jeffqchen/Famicom-Expansion-Port-Switcher/pics/Famicom/GPM/case_crack_01.jpg

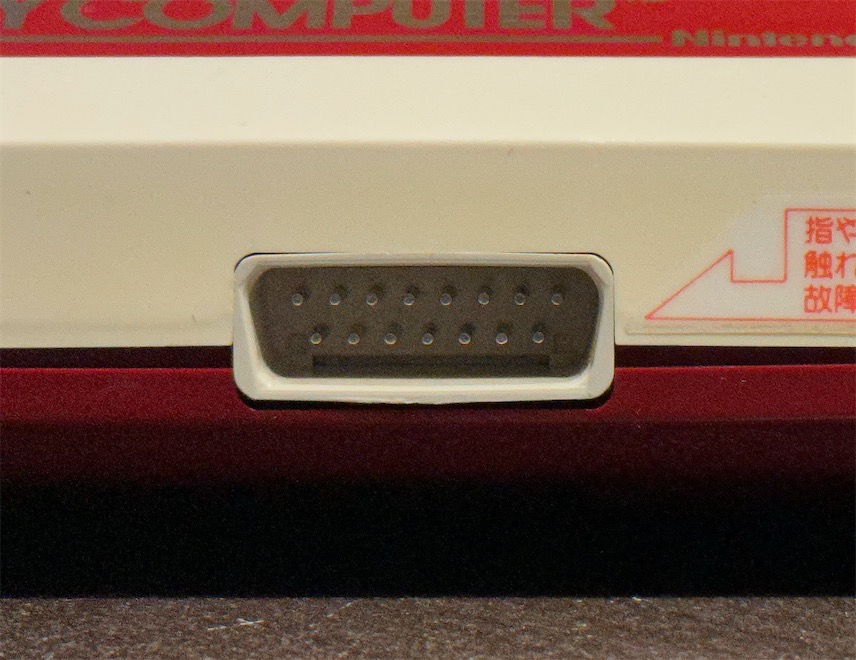
pics/Famicom/GPM/case_crack_01.jpg
