jeffqchen/Famicom-Expansion-Port-Switcher/pics/Famicom/GPM/case_crack_02.jpg

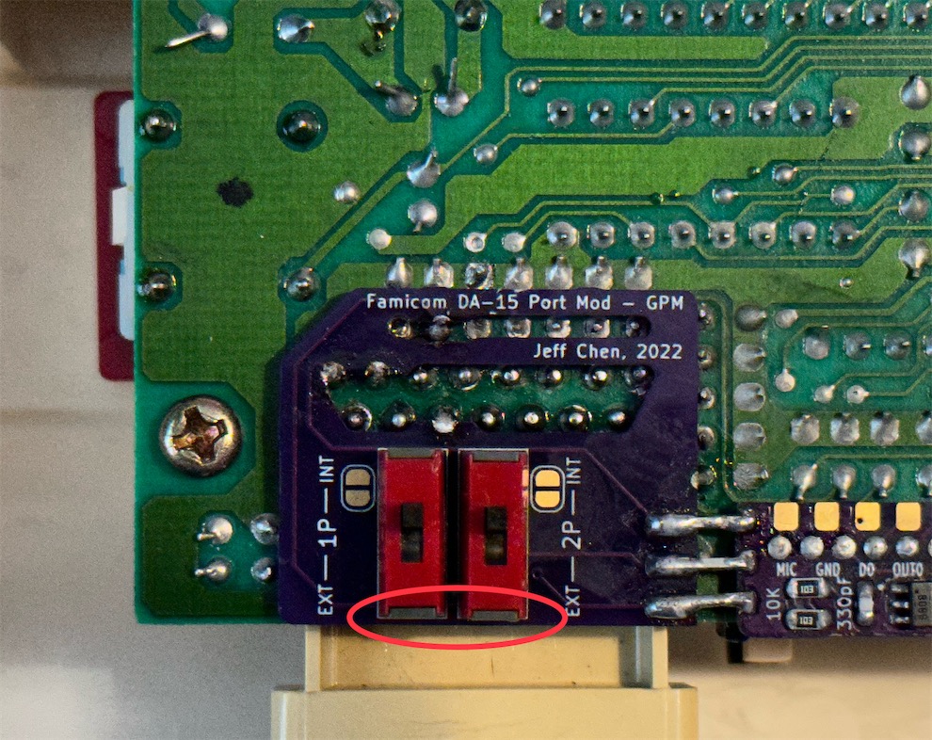
pics/Famicom/GPM/case_crack_02.jpg
