jeffqchen/Famicom-Expansion-Port-Switcher/pics/Famicom/GPM/cuttrace.jpg

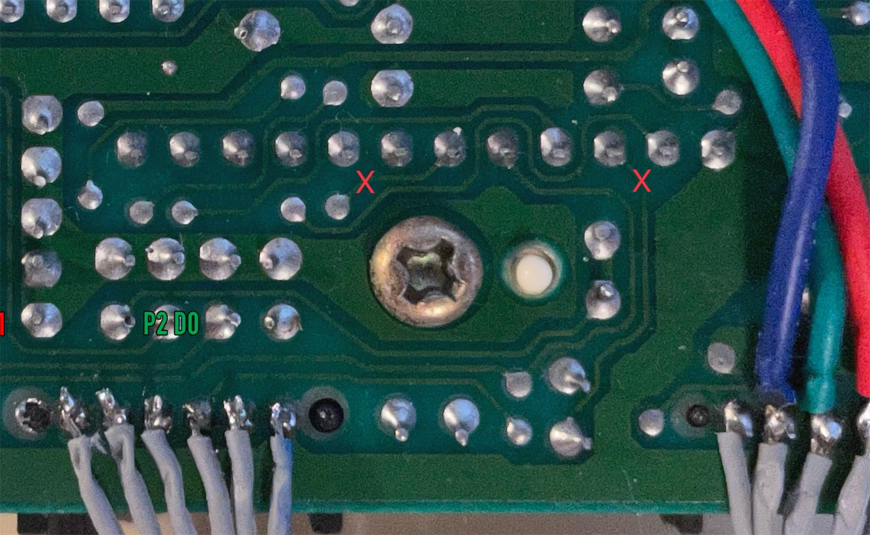
pics/Famicom/GPM/cuttrace.jpg
