jeffqchen/Famicom-Expansion-Port-Switcher/pics/Famicom/GPM/da15_isolate.jpg

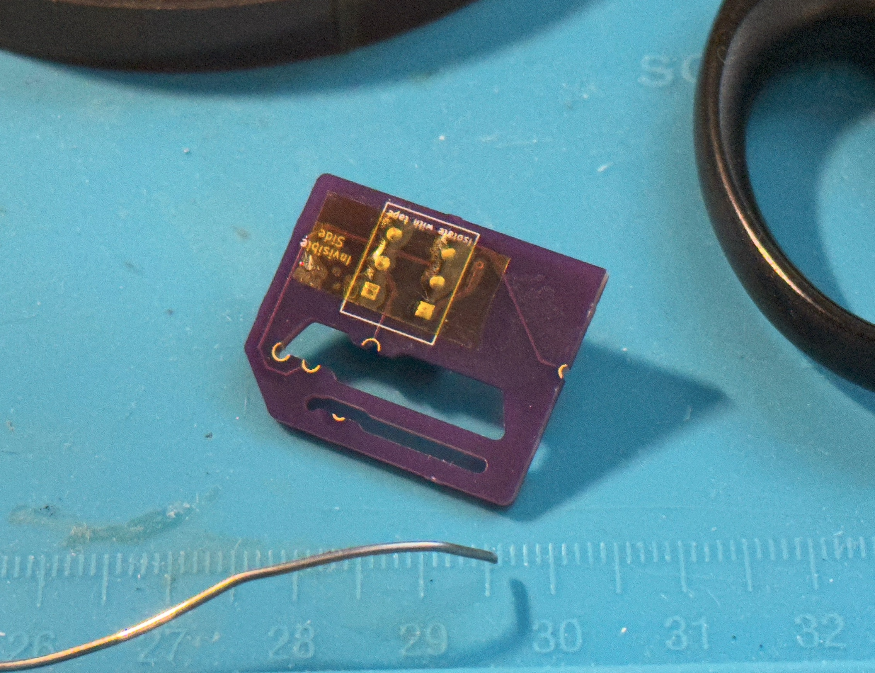
pics/Famicom/GPM/da15_isolate.jpg
