jeffqchen/Famicom-Expansion-Port-Switcher/pics/Famicom/GPM/da15_populate.jpg

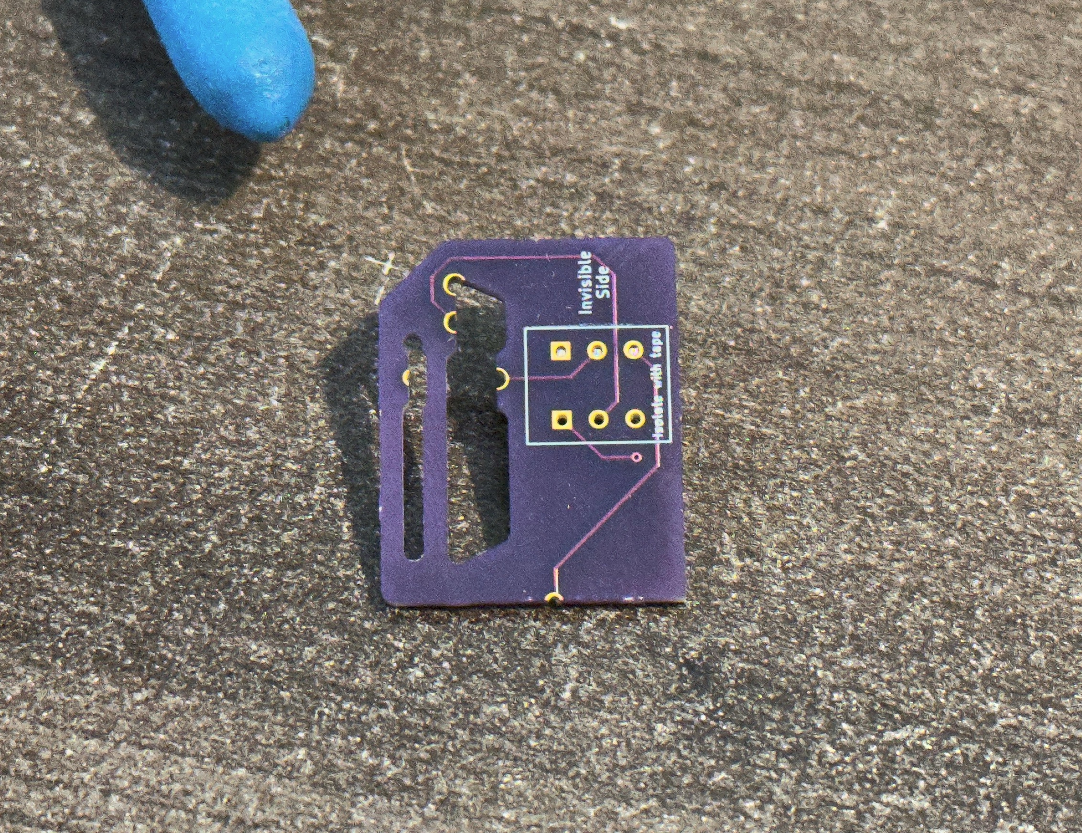
pics/Famicom/GPM/da15_populate.jpg
