jeffqchen/Famicom-Expansion-Port-Switcher/pics/Famicom/GPM/drill_01_intention.jpg

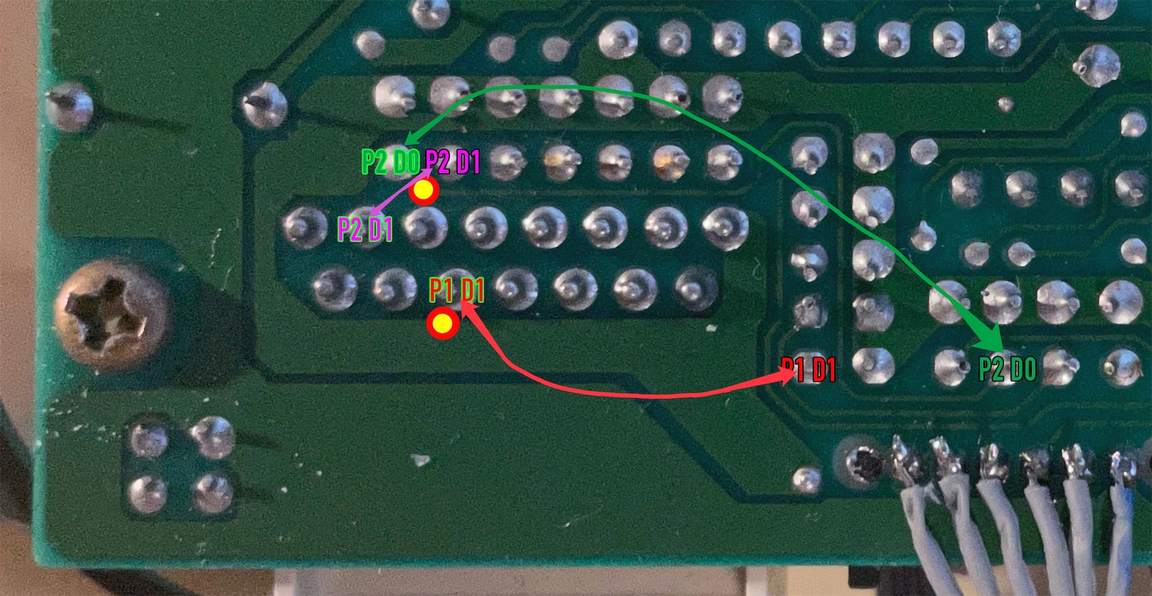
pics/Famicom/GPM/drill_01_intention.jpg
