jeffqchen/Famicom-Expansion-Port-Switcher/pics/Famicom/GPM/drill_02_withjig.jpg

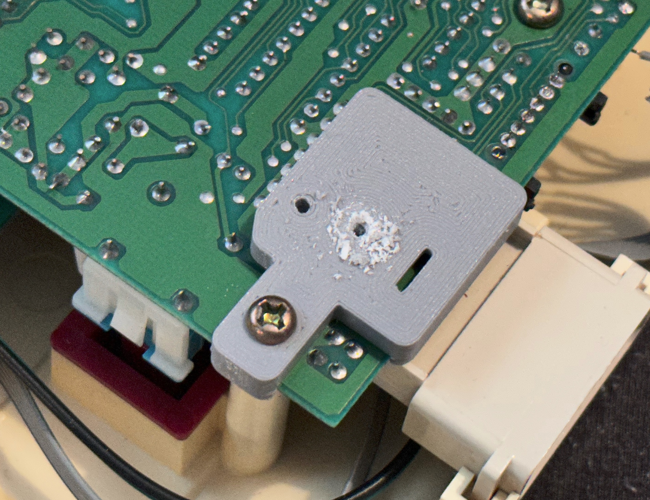
pics/Famicom/GPM/drill_02_withjig.jpg
