jeffqchen/Famicom-Expansion-Port-Switcher/pics/Famicom/GPM/drill_03_afterwards.jpg

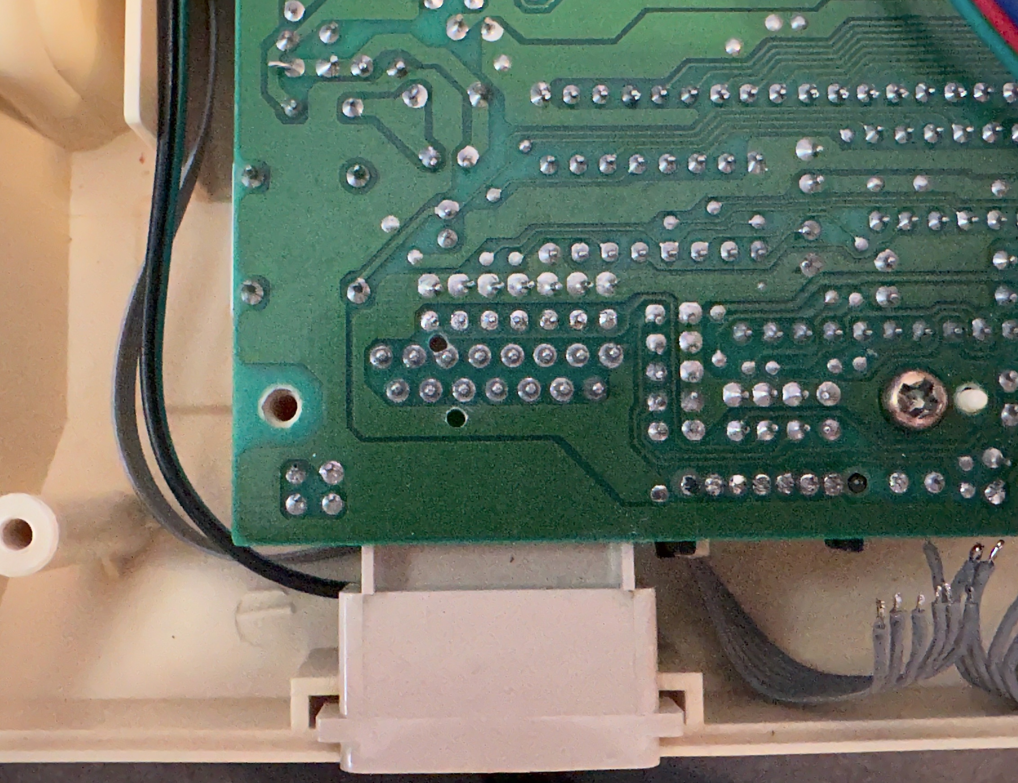
pics/Famicom/GPM/drill_03_afterwards.jpg
