jeffqchen/Famicom-Expansion-Port-Switcher/pics/Famicom/GPM/dryfit_02.jpg

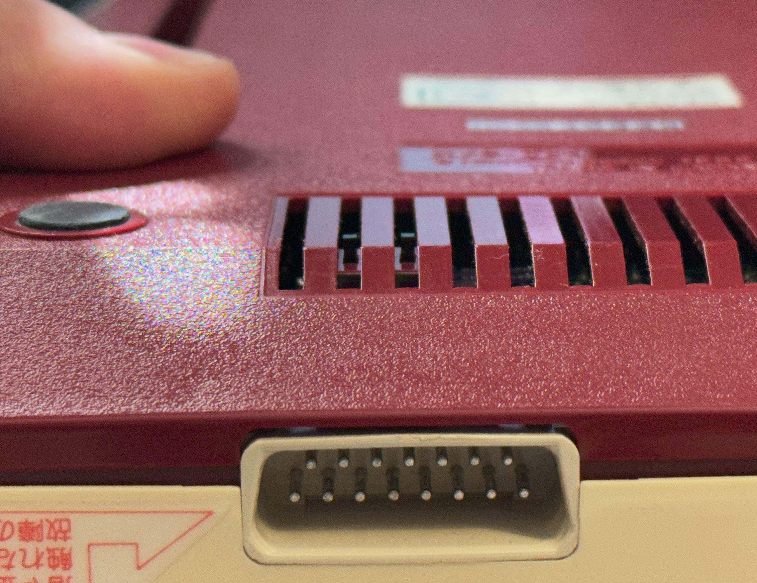
pics/Famicom/GPM/dryfit_02.jpg
