jeffqchen/Famicom-Expansion-Port-Switcher/pics/Famicom/GPM/finish.jpg

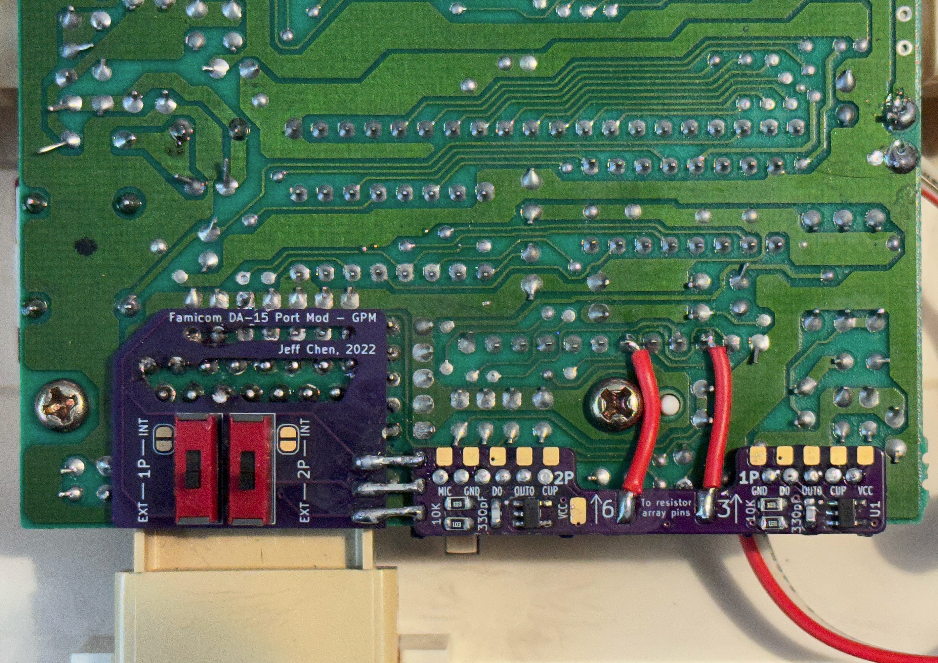
pics/Famicom/GPM/finish.jpg
