jeffqchen/Famicom-Expansion-Port-Switcher/pics/Famicom/GPM/functionality.jpg

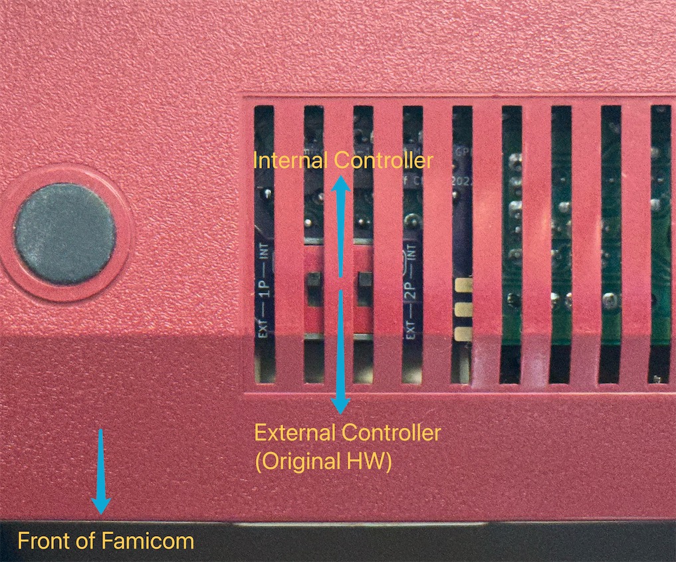
pics/Famicom/GPM/functionality.jpg
