jeffqchen/Famicom-Expansion-Port-Switcher/pics/Famicom/GPM/internalpcb_hack.jpg

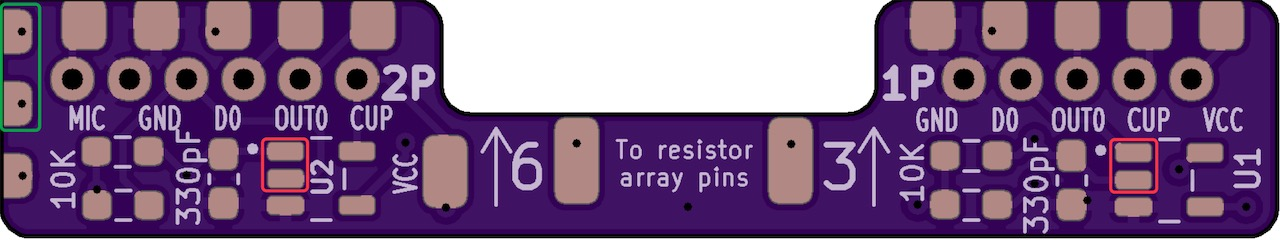
pics/Famicom/GPM/internalpcb_hack.jpg
