jeffqchen/Famicom-Expansion-Port-Switcher/pics/Famicom/GPM/internalpcb_populate.jpg

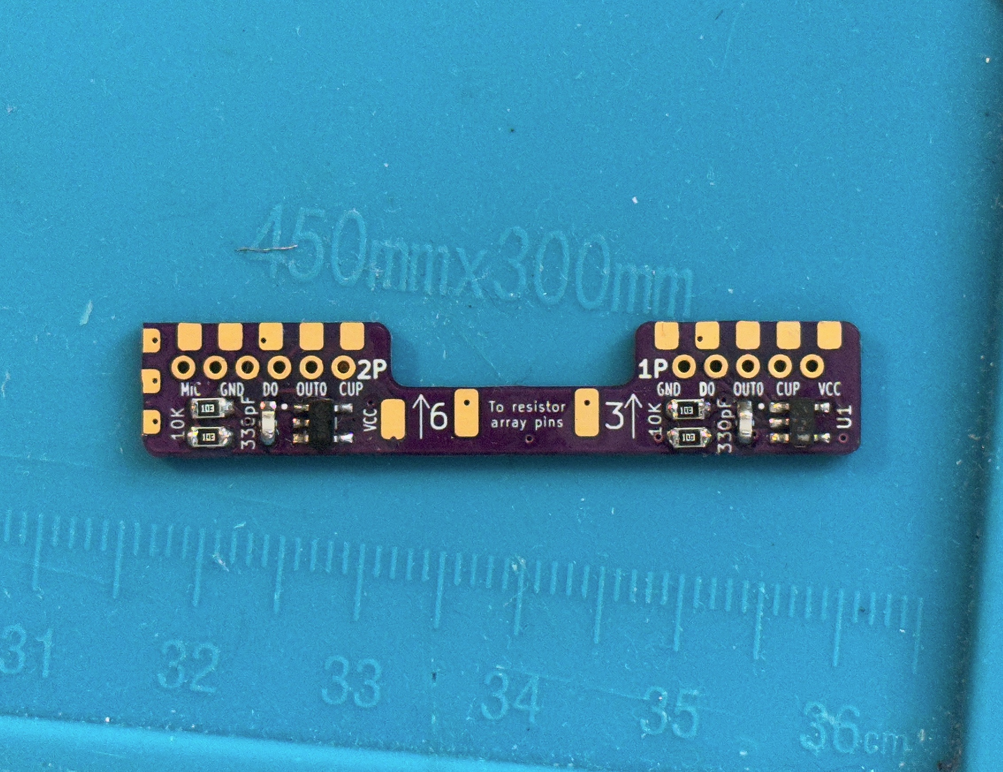
pics/Famicom/GPM/internalpcb_populate.jpg
