jeffqchen/Famicom-Expansion-Port-Switcher/pics/Famicom/GPM/jig.jpg

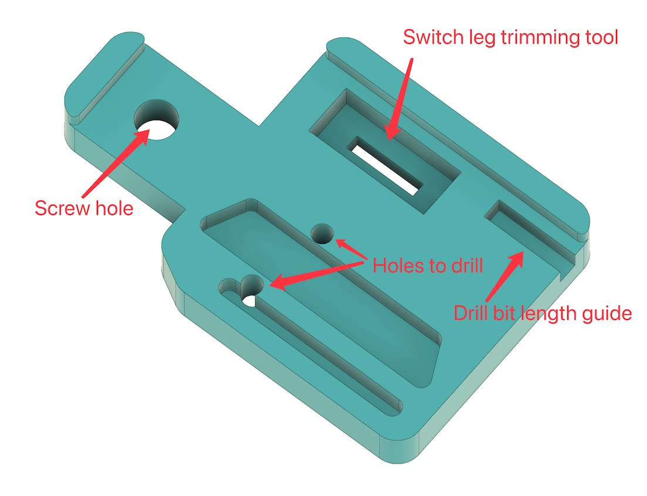
pics/Famicom/GPM/jig.jpg
