jeffqchen/Famicom-Expansion-Port-Switcher/pics/Famicom/GPM/straightenpins_02.jpg

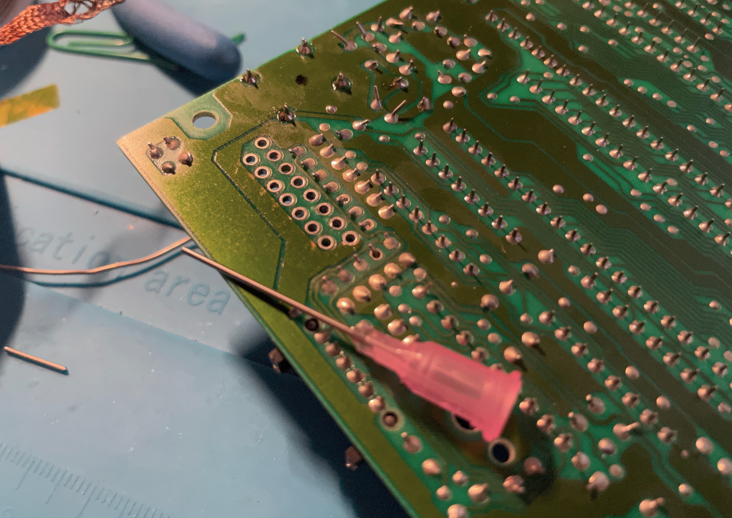
pics/Famicom/GPM/straightenpins_02.jpg
