jeffqchen/Famicom-Expansion-Port-Switcher/pics/Famicom/GPM/straightenpins_03.jpg

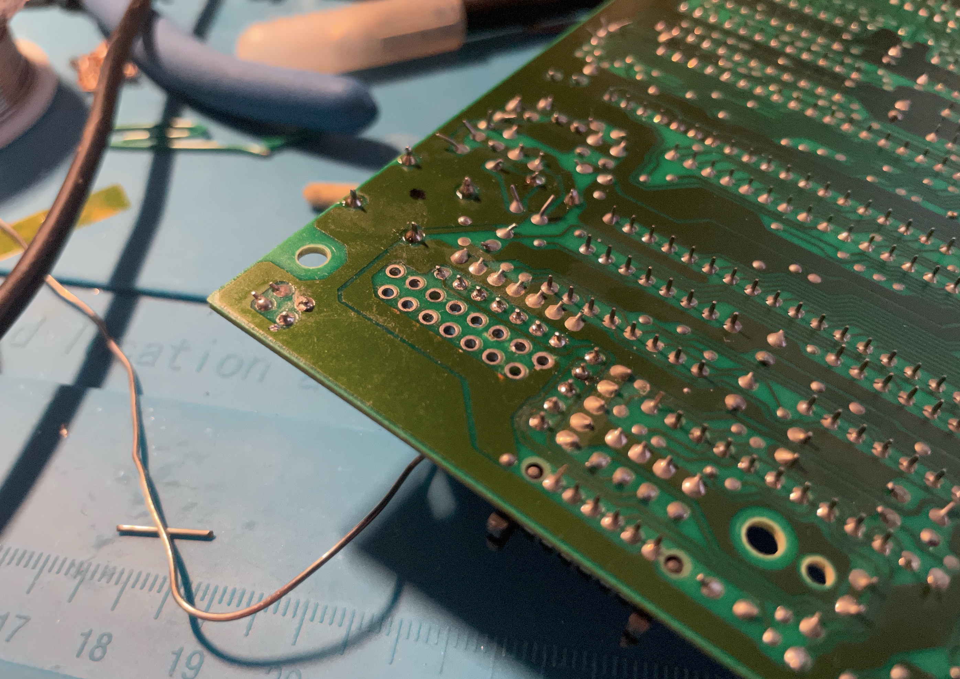
pics/Famicom/GPM/straightenpins_03.jpg
