jeffqchen/Famicom-Expansion-Port-Switcher/pics/Famicom/GPM/trim_01.jpg

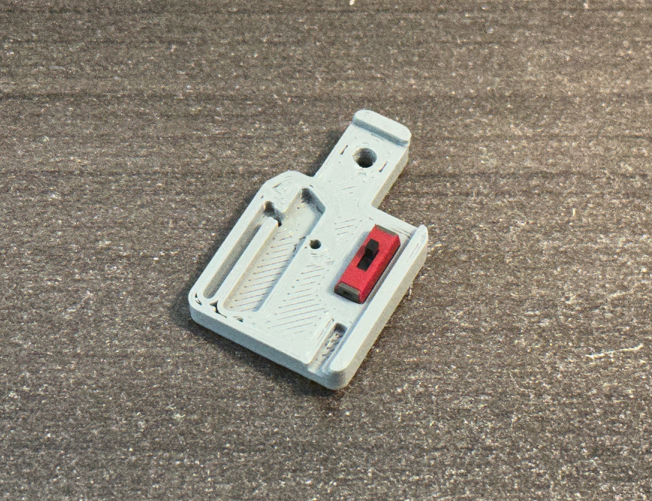
pics/Famicom/GPM/trim_01.jpg
