jeffqchen/Famicom-Expansion-Port-Switcher/pics/front_expansion.jpg

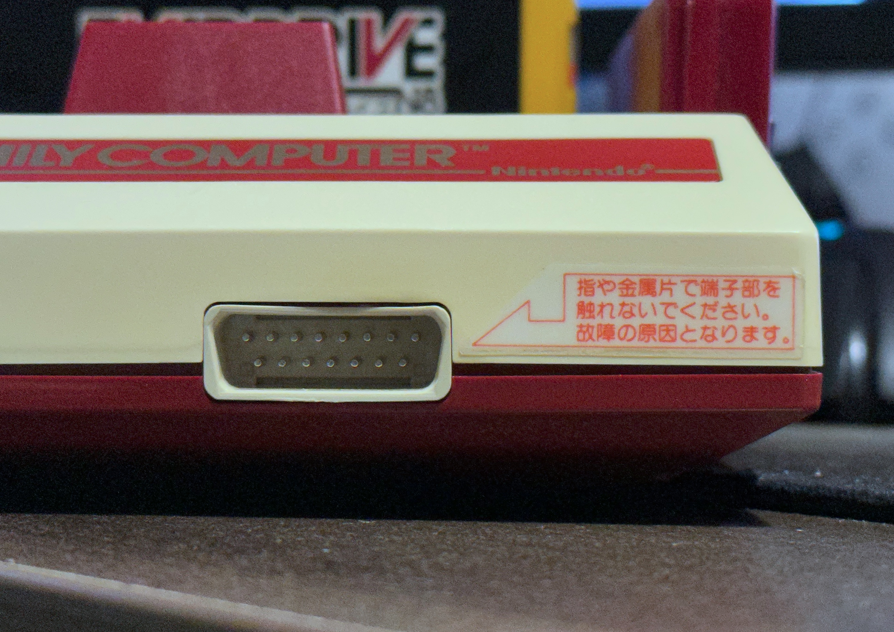
pics/front_expansion.jpg
