jeffqchen/Famicom-Expansion-Port-Switcher/pics/Twins/functionality.jpg

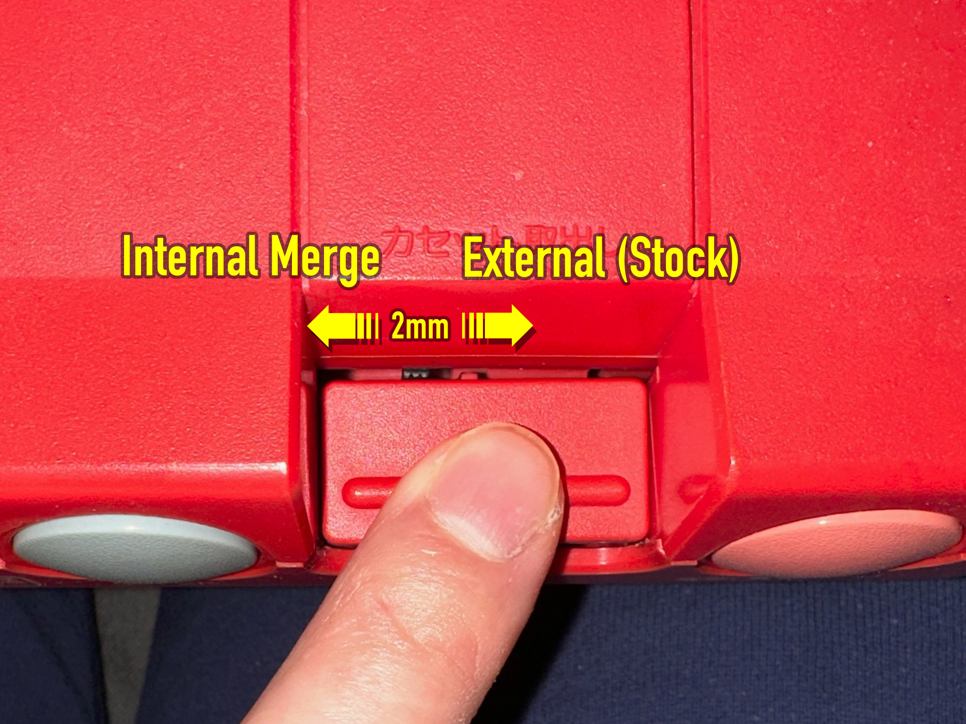
pics/Twins/functionality.jpg
