jeffqchen/Famicom-Expansion-Port-Switcher/pics/Twins/main_PCB.png

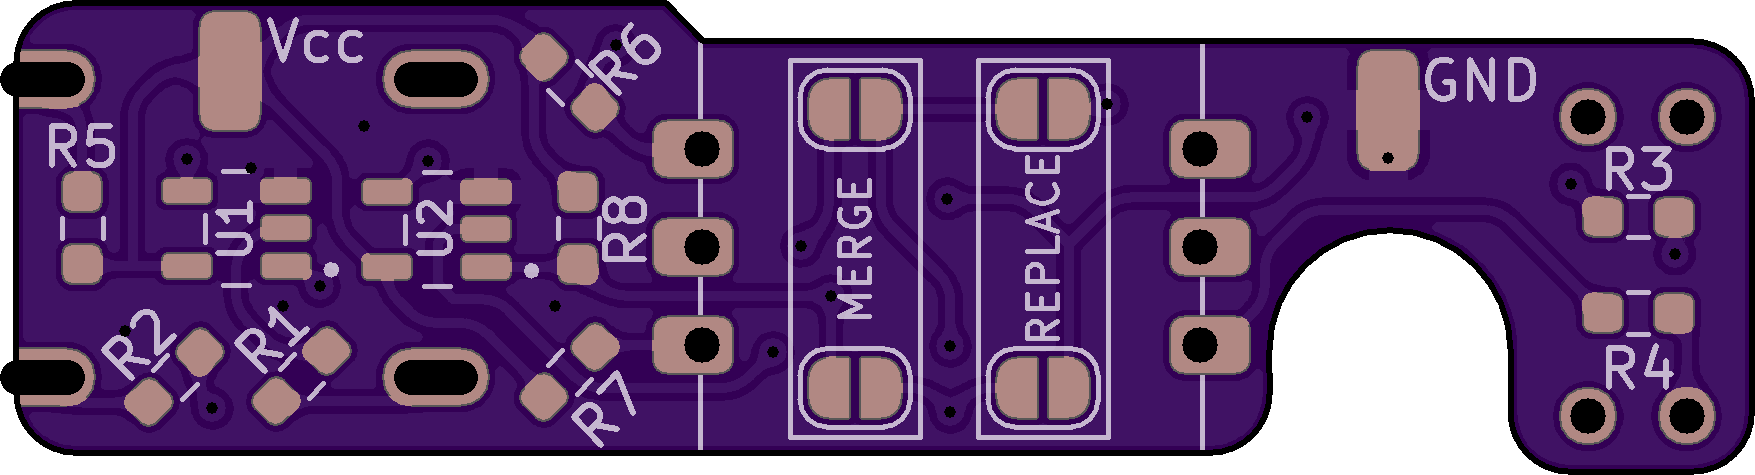
pics/Twins/main_PCB.png
