jeffqchen/Famicom-Expansion-Port-Switcher/pics/Twins/misc.jpg

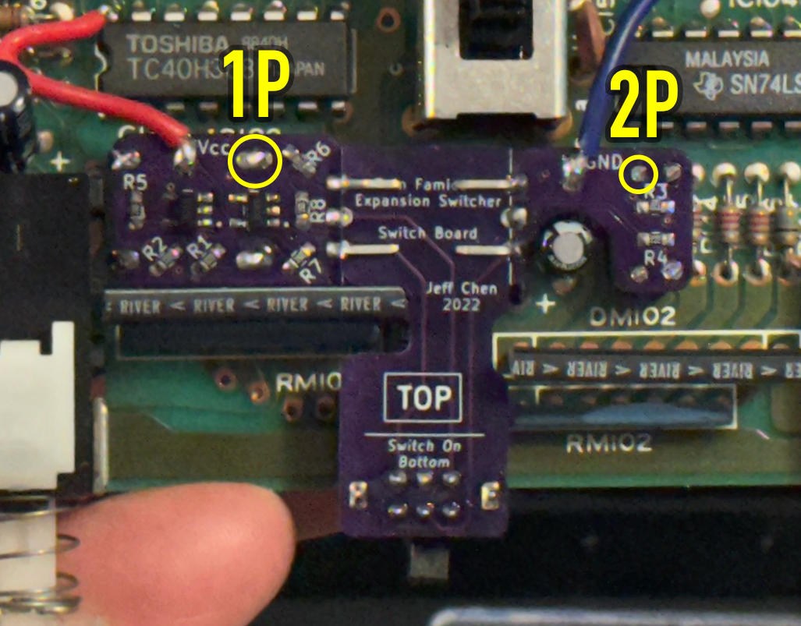
pics/Twins/misc.jpg
