jeffqchen/Famicom-Expansion-Port-Switcher/pics/Twins/optional_pin_01.jpg

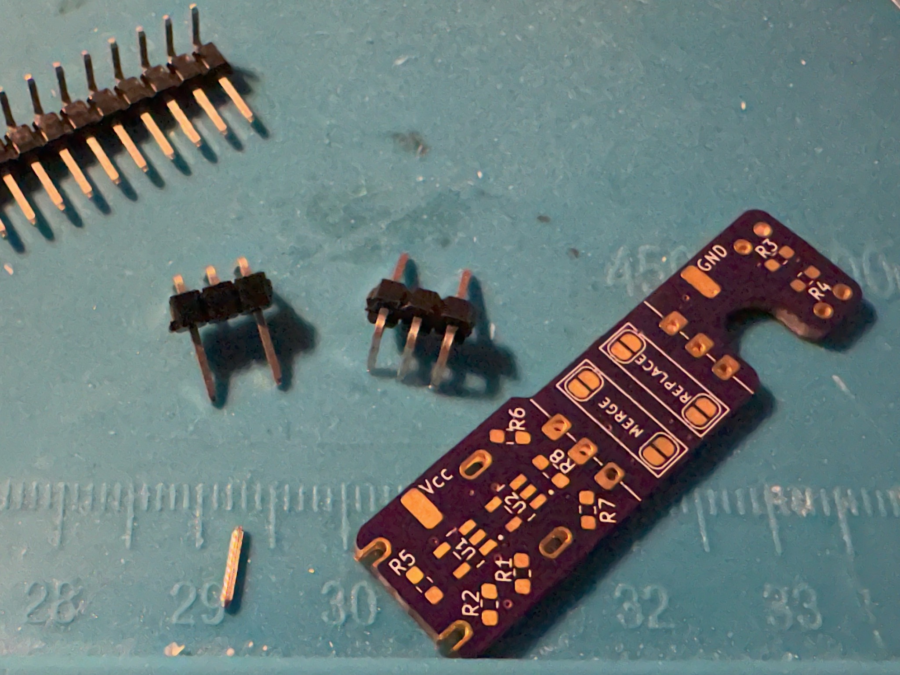
pics/Twins/optional_pin_01.jpg
