jeffqchen/Famicom-Expansion-Port-Switcher/pics/Twins/optional_pin_03.jpg

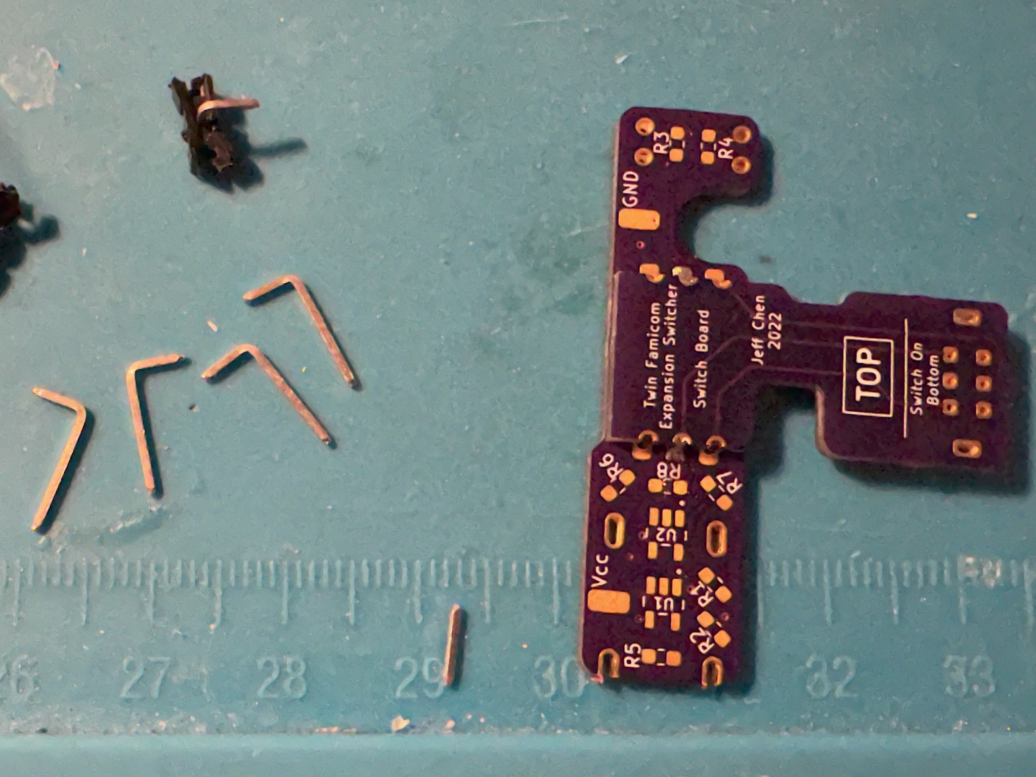
pics/Twins/optional_pin_03.jpg
