jeffqchen/Famicom-Expansion-Port-Switcher/pics/Twins/optional_pin_04.jpg

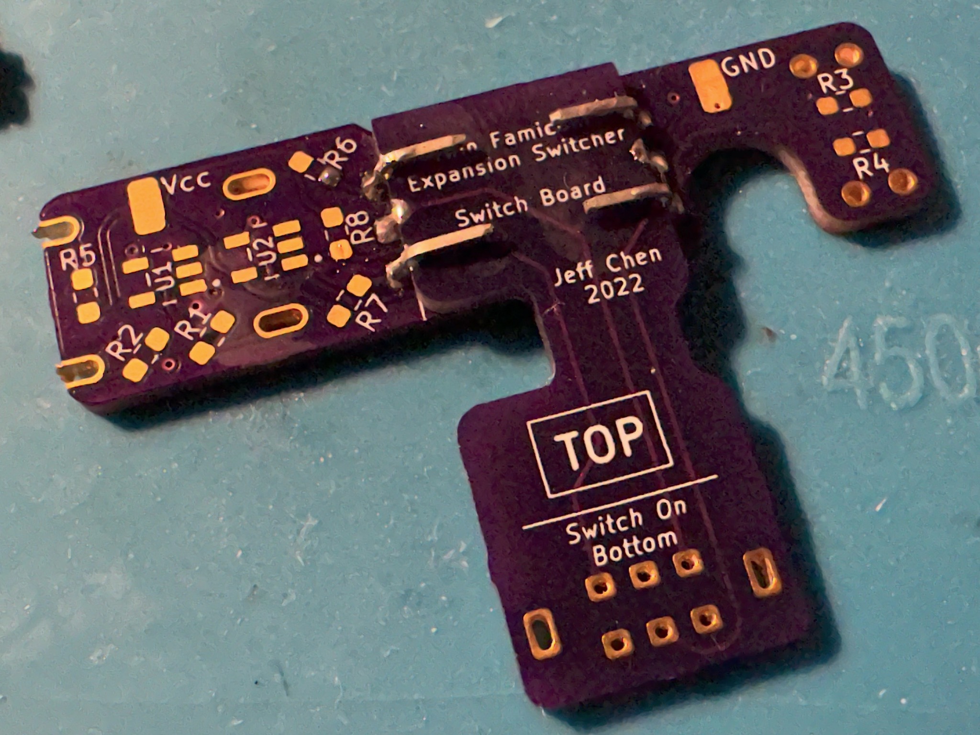
pics/Twins/optional_pin_04.jpg
