jeffqchen/Famicom-Expansion-Port-Switcher/pics/Twins/optional_pin_05.jpg

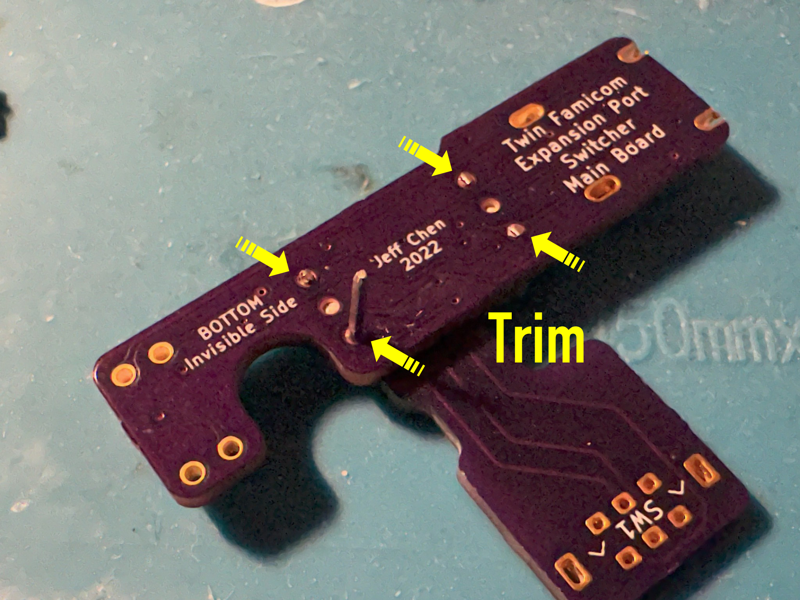
pics/Twins/optional_pin_05.jpg
