jeffqchen/Famicom-Expansion-Port-Switcher/pics/Twins/populate_03.jpg

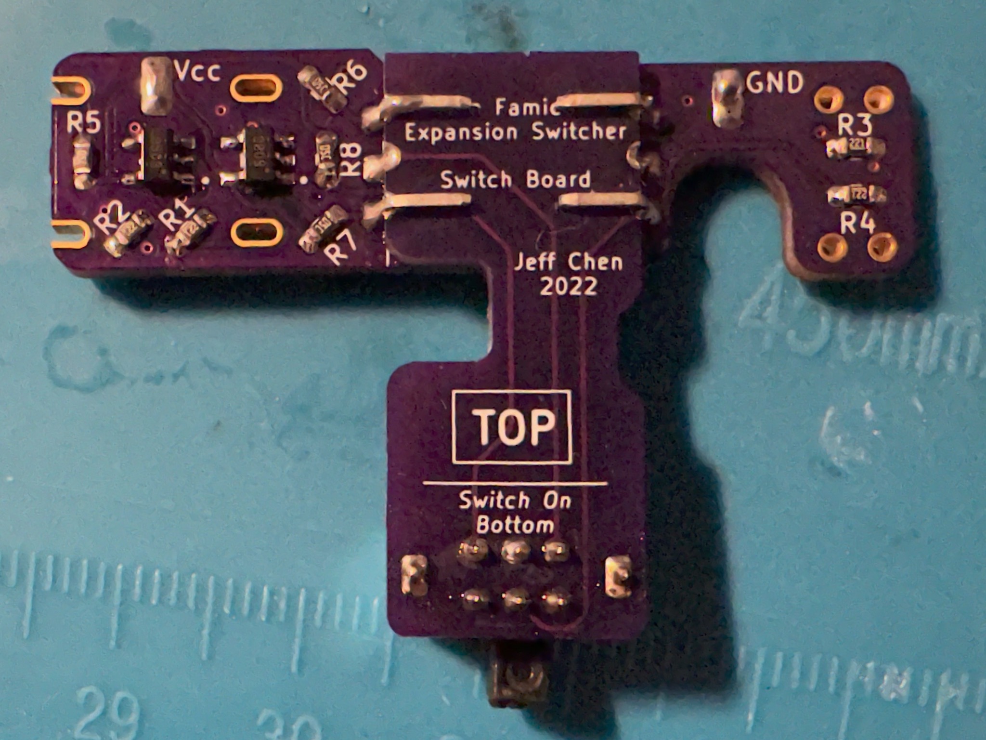
pics/Twins/populate_03.jpg
