jeffqchen/Famicom-Expansion-Port-Switcher/pics/Twins/prepare_pcb.jpg

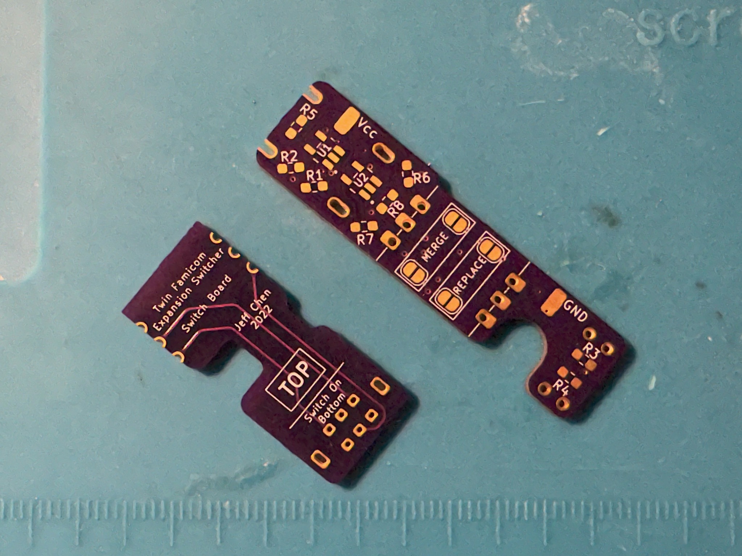
pics/Twins/prepare_pcb.jpg
