jeffqchen/Famicom-Expansion-Port-Switcher/pics/Famicom/GPM/da15_solder_in.jpg

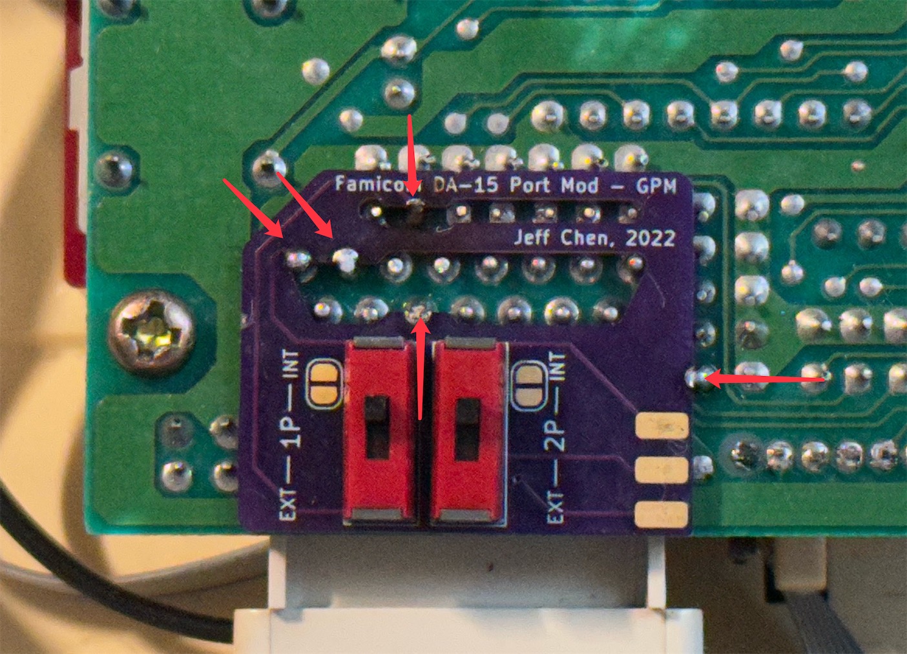
pics/Famicom/GPM/da15_solder_in.jpg
