jeffqchen/Famicom-Expansion-Port-Switcher/pics/Twins/install_01.jpg

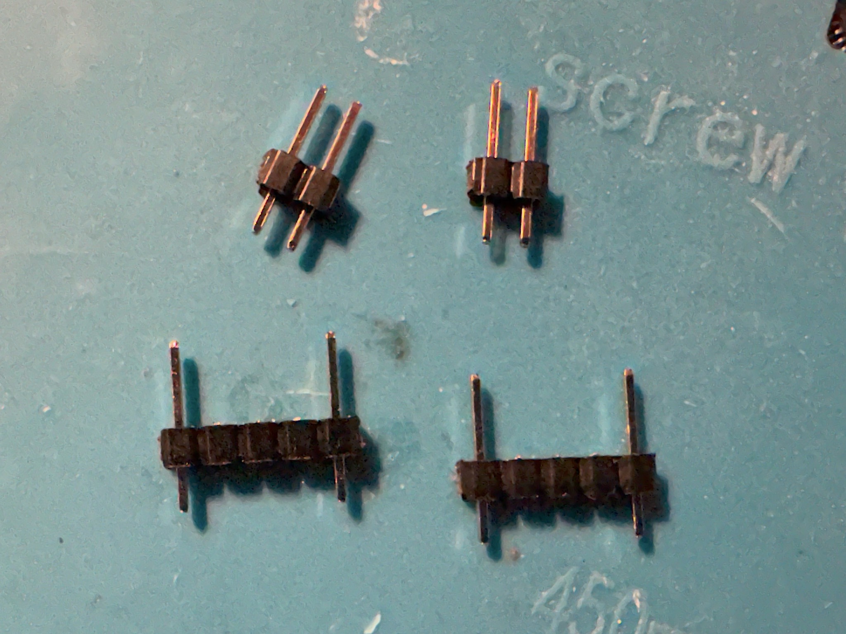
pics/Twins/install_01.jpg
