jeffqchen/Famicom-Expansion-Port-Switcher/pics/Twins/install_02.jpg

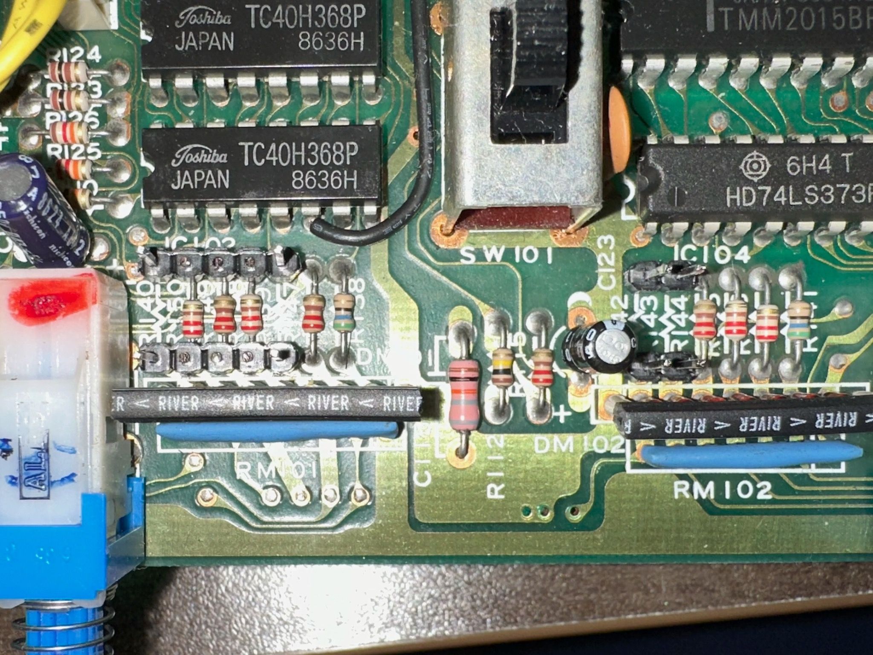
pics/Twins/install_02.jpg
