jeffqchen/Famicom-Expansion-Port-Switcher/pics/Twins/install_03.jpg

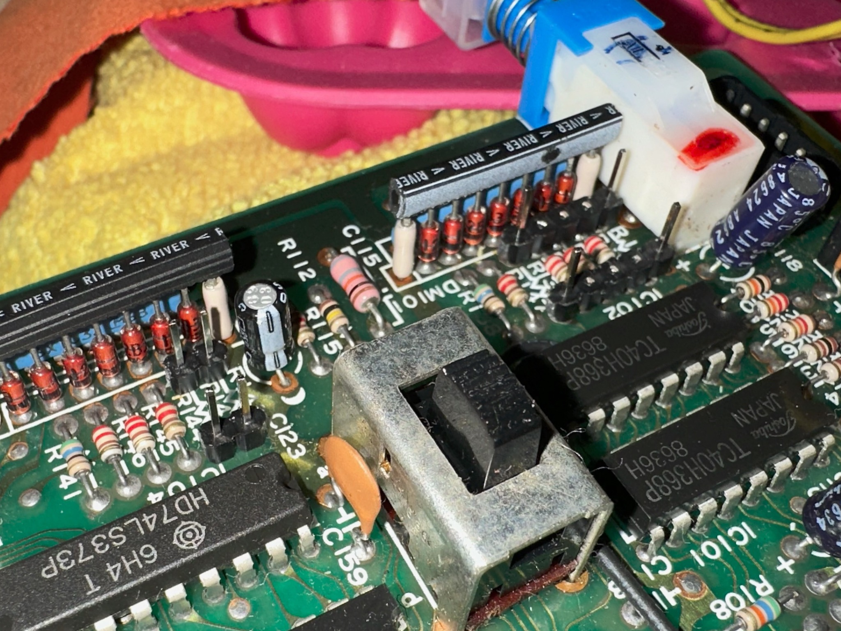
pics/Twins/install_03.jpg
