jeffqchen/Famicom-Expansion-Port-Switcher/pics/Twins/install_04.jpg

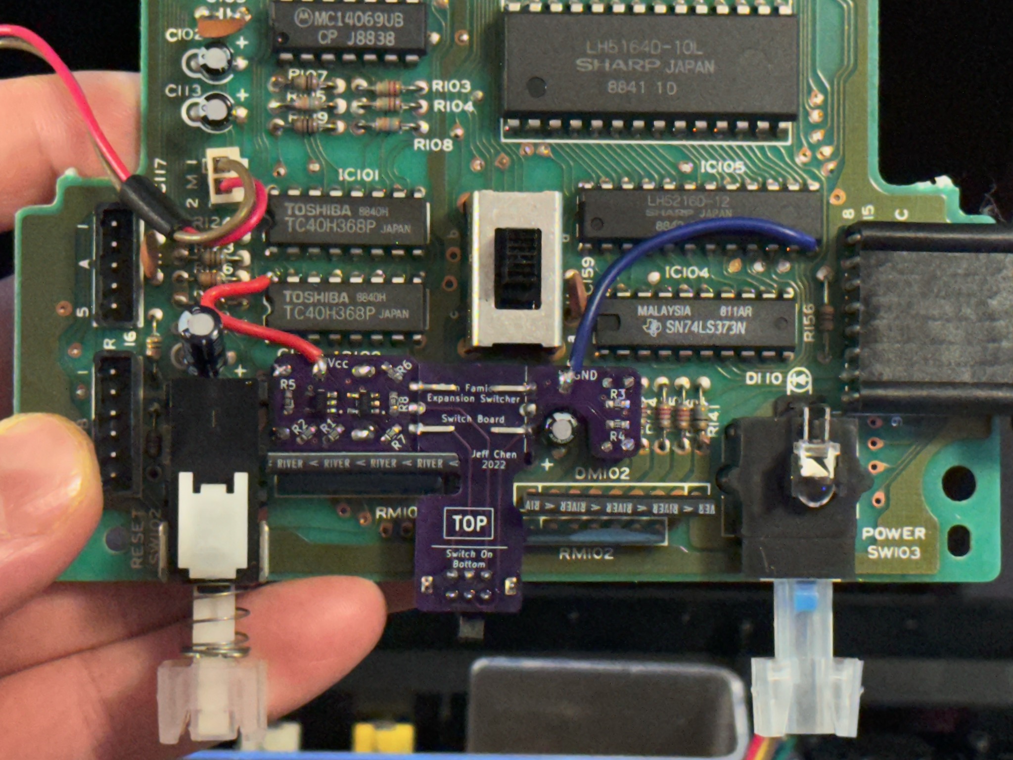
pics/Twins/install_04.jpg
