jeffqchen/Famicom-Expansion-Port-Switcher/pics/Twins/install_05.jpg

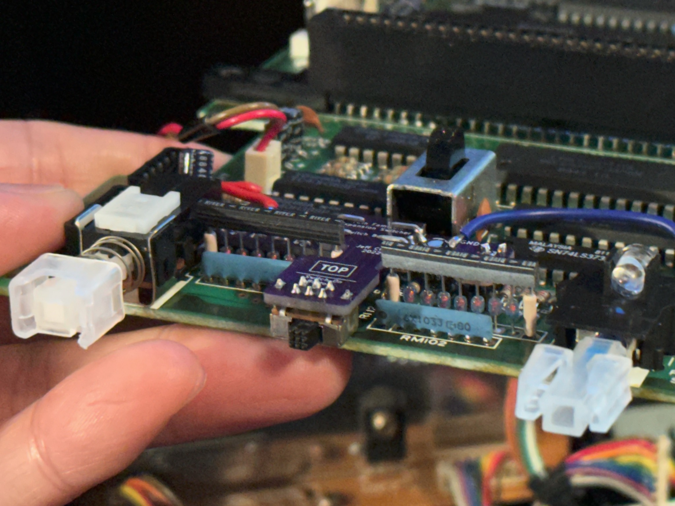
pics/Twins/install_05.jpg
