jeffqchen/Famicom-Expansion-Port-Switcher/pics/Twins/PCB_solder.jpg

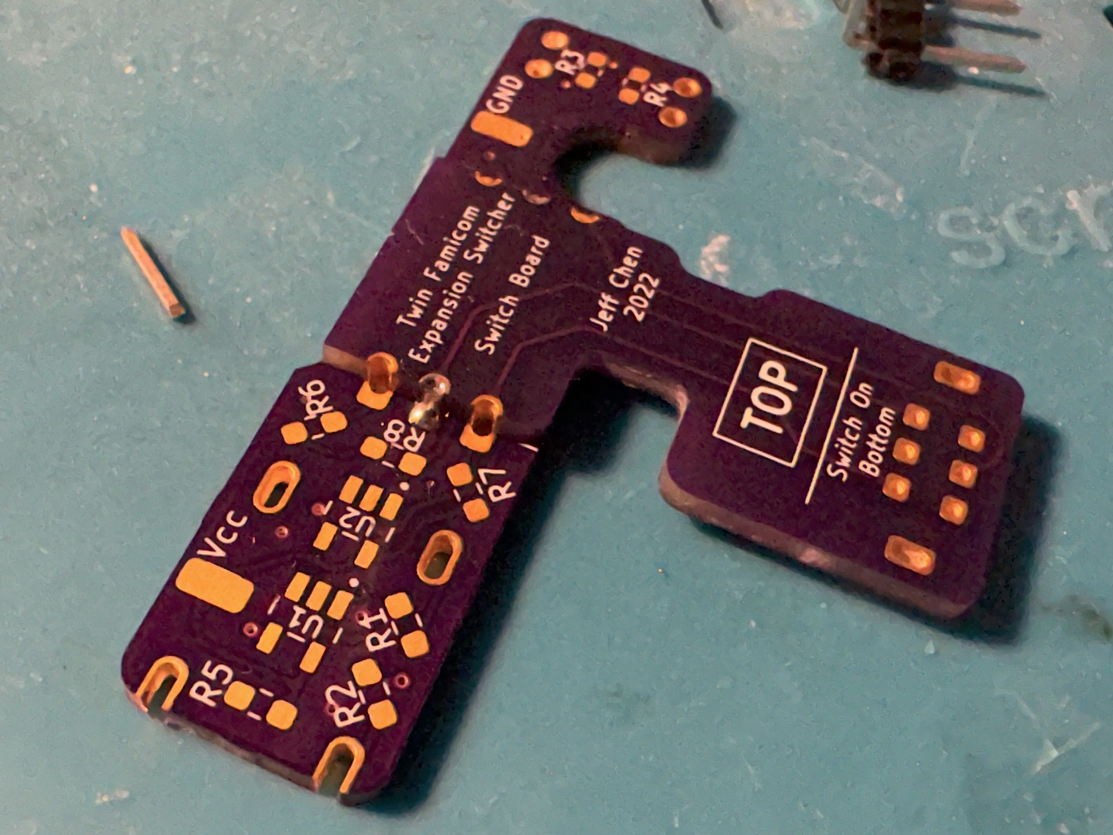
pics/Twins/PCB_solder.jpg
